Mlevike/okos-belepteto-rendszer/documentation/images/belepteto_show_denied_message.jpg

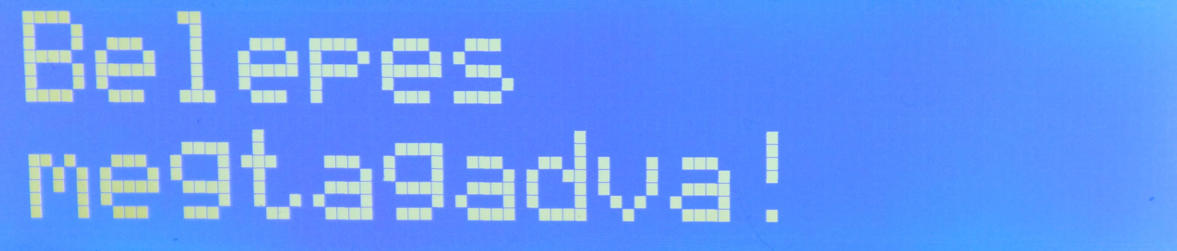
documentation/images/belepteto_show_denied_message.jpg
